papayapeter/head/processing/processing/Animation_Data.h

const byte FPS = 10;
const int Animation_Length = 735;
const byte Animation_Sequence[Animation_Length][3] = {
{255, 255, 60}, 
{255, 255, 60}, 
{255, 255, 60}, 
{255, 255, 60}, 
{255, 255, 60}, 
{255, 255, 60}, 
{255, 255, 60}, 
{255, 255, 63}, 
{255, 255, 63}, 
{255, 255, 67}, 
{255, 255, 67}, 
{255, 255, 67}, 
{255, 255, 67}, 
{255, 255, 67}, 
{255, 255, 67}, 
{255, 255, 67}, 
{255, 255, 67}, 
{255, 255, 67}, 
{255, 255, 67}, 
{255, 255, 67}, 
{255, 255, 67}, 
{255, 255, 67}, 
{255, 255, 67}, 
{255, 255, 67}, 
{255, 255, 67}, 
{255, 255, 67}, 
{255, 255, 67}, 
{255, 255, 67}, 
{255, 255, 63}, 
{255, 255, 63}, 
{255, 255, 63}, 
{255, 255, 63}, 
{255, 255, 67}, 
{255, 255, 67}, 
{255, 255, 67}, 
{255, 255, 71}, 
{255, 255, 71}, 
{255, 255, 71}, 
{255, 255, 71}, 
{255, 255, 71}, 
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
};
