papayapeter/head/teensy/run/Animation_Data.h

const byte FPS = 10;
const int Animation_Length = 735;
const byte Animation_Sequence[Animation_Length][3] = {
{247, 252, 60}, 
{247, 252, 60}, 
{247, 252, 60}, 
{247, 252, 60}, 
{247, 252, 60}, 
{246, 251, 60}, 
{246, 251, 60}, 
{246, 251, 63}, 
{245, 251, 63}, 
{246, 251, 67}, 
{245, 251, 67}, 
{245, 251, 67}, 
{244, 251, 67}, 
{245, 251, 67}, 
{244, 251, 67}, 
{244, 251, 67}, 
{244, 251, 67}, 
{244, 251, 67}, 
{243, 251, 67}, 
{243, 251, 67}, 
{243, 251, 67}, 
{243, 251, 67}, 
{243, 251, 67}, 
{243, 251, 67}, 
{243, 251, 67}, 
{243, 251, 67}, 
{242, 251, 67}, 
{242, 251, 67}, 
{242, 251, 63}, 
{242, 251, 63}, 
{241, 251, 63}, 
{241, 251, 63}, 
{241, 251, 67}, 
{241, 251, 67}, 
{240, 251, 67}, 
{240, 251, 71}, 
{240, 251, 71}, 
{240, 251, 71}, 
{239, 251, 71}, 
{239, 251, 71}, 
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
};
